bochoa510/projectPSI/Resources/ADS1115/README.md

# Main Resource

* https://how2electronics.com/how-to-use-ads1115-16-bit-adc-module-with-arduino/
