bochoa510/projectPSI/Resources/ADS1115/Hardware/README.md

# ADS1115 Resources Used

* https://how2electronics.com/how-to-use-ads1115-16-bit-adc-module-with-arduino/

* Parts described in schematic
  - 2x MMZ2012Y152B, Ferrite Beads Multi-Layer 1.5KOhm 25% 100MHz 500mA 400mOhm
  - 2x 1uF Cap
  - 4x 10kOhm Resistor
