bochoa510/projectPSI/Resources/ADS1115/Code/README.md

# Resources Used for ADS1115

* https://how2electronics.com/how-to-use-ads1115-16-bit-adc-module-with-arduino/
