bochoa510/projectPSI/Previous versions/rev2/README.md

# for Rev3 fix layout design problems:

   I2C pins, pull up resistors
   
   pull down resistors for transistors

# for Rev3 goal is to have self contained pcb:

  5v relay moodule w/ isolation
  
  16bit adc module 

# I would like to include surface mount components:

  capacitors
  
  resistors
  
  diodes
  
  atmega328p (maybe)
  
  # projectPSI ; Automatic Tire Inflator

arduino code  : mainControl.ino 

schematic & layout files : pPSI.zip

# Materials
1: Stepdown transformer 120V -> 24V (https://www.digikey.com/en/products/detail/triad-magnetics/TCT40-01E07K/666127)

2: 24V AC N/C Solenoid Valve 1/2" (https://www.electricsolenoidvalves.com/1-2-24v-ac-electric-brass-solenoid-valve/)

2: AC->DC converter, 5V (https://www.amazon.com/gp/product/B07V5XP92F/ref=ppx_yo_dt_b_asin_title_o03_s00?ie=UTF8&psc=1)

  

    - C1: 47μF/25V electrolytic capacitor
    - C2: 1μF/50V ceramic capacitor (105)
    - D1: TVS 7A diode 

2: 5V relay modules (https://www.amazon.com/dp/B00LW15A4W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) 

1: Atmega328pu (https://www.digikey.com/en/products/detail/microchip-technology/ATMEGA328P-PU/1914589)

    - 2: 22pF ceramic capacitor (220)
    - 1: 16MHz crystal oscillator

1: 150 PSI Pressure Transducer (https://www.amazon.com/dp/B08G4YRZT8/ref=twister_B08G4XH5PK?_encoding=UTF8&psc=1)

1: ADS1115 16bit ADC board  (https://www.amazon.com/dp/B08HLWLR77?psc=1&ref=ppx_yo2ov_dt_b_product_details)

4: NPN Transistors 

2: 74HC595N Shift Register (https://www.digikey.com/en/products/detail/texas-instruments/SN74HC595N/277246)

    - 2: .1μF ceramic capacitor (104)

2: 1" 7 Segment LED Display (https://www.mouser.com/ProductDetail/604-SC10-21SRWA)
